hugoescalpelo/Bodies-of-Potentials/STL/Calamar - Motor Tester v3.stl

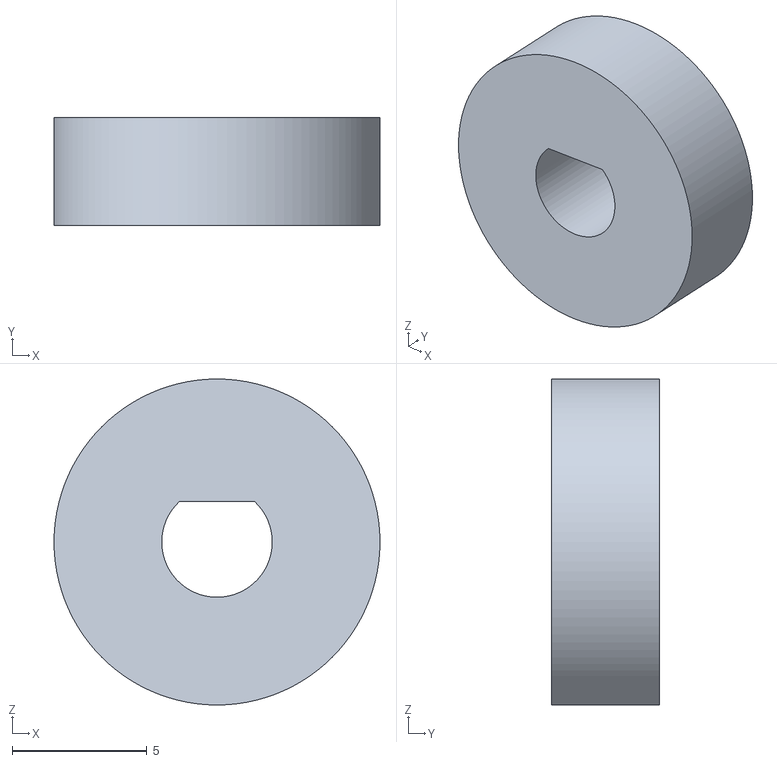
[picture p17: CAD file, 2025-03-10]
STL/Calamar - Motor Tester v3.stl
12.1 x 4.00 x 12.1
