hugoescalpelo/Bodies-of-Potentials/STL/Base Integral v26.stl

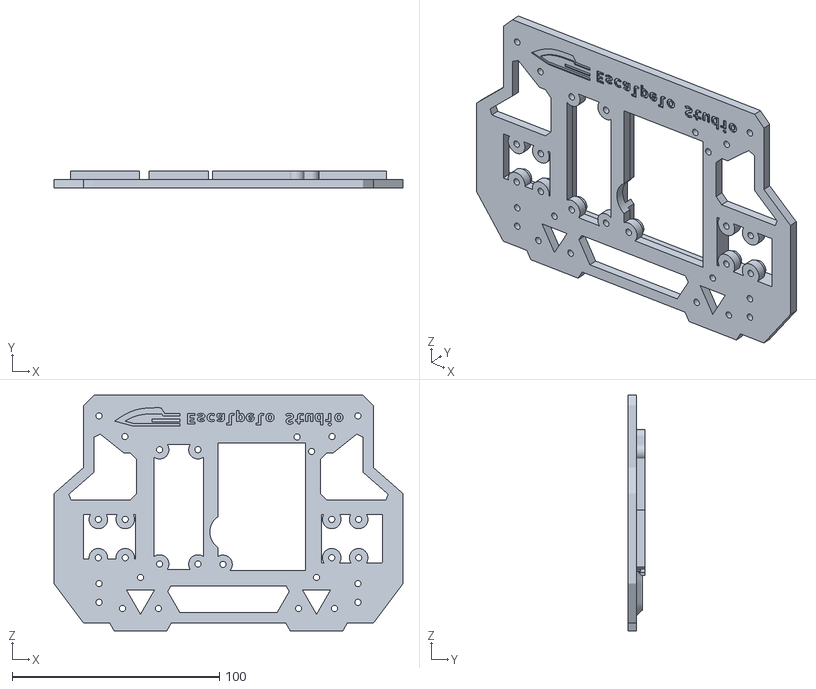
[picture p18: CAD file, 2025-03-10]
STL/Base Integral v26.stl
168.5 x 8.00 x 113.8
