hugoescalpelo/Bodies-of-Potentials/STL/Calamar_New_DC_Motor v7.stl

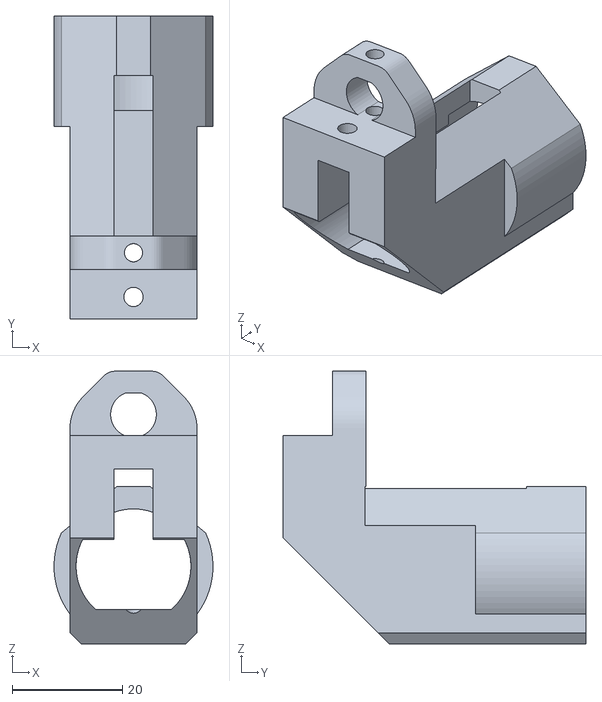
[picture p19: CAD file, 2025-03-10]
STL/Calamar_New_DC_Motor v7.stl
28.8 x 54.9 x 49.4
