hugoescalpelo/Bodies-of-Potentials/STL/plate adapter v2.stl

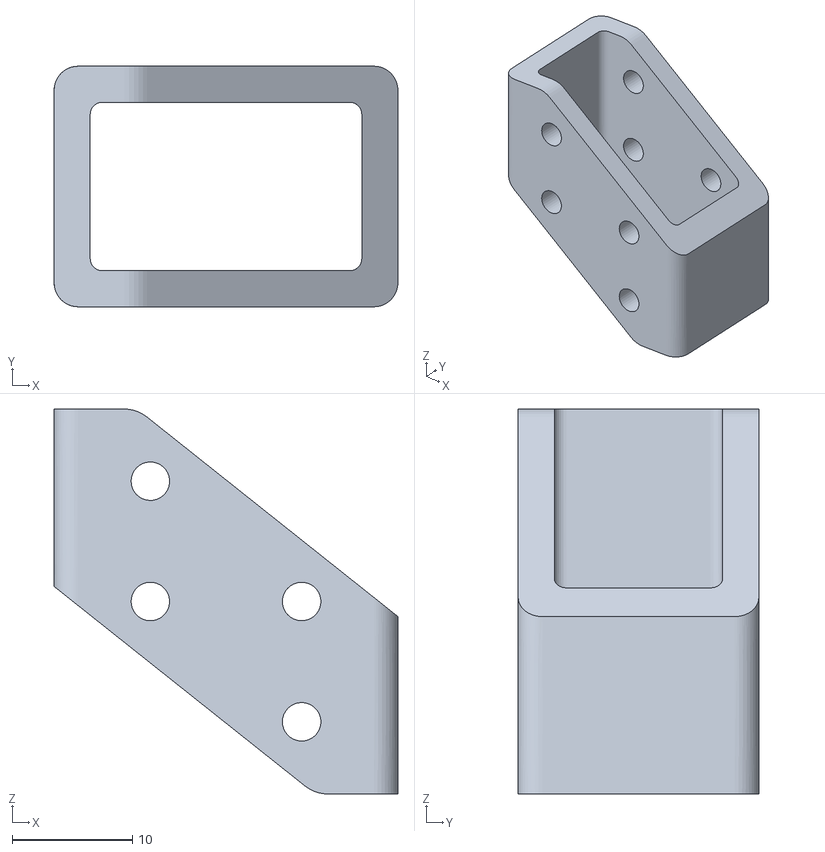
[picture p20: CAD file, 2025-03-10]
STL/plate adapter v2.stl
28.6 x 20.0 x 32.0
