hugoescalpelo/Bodies-of-Potentials/STL/Brazo nuevo Calamar.stl

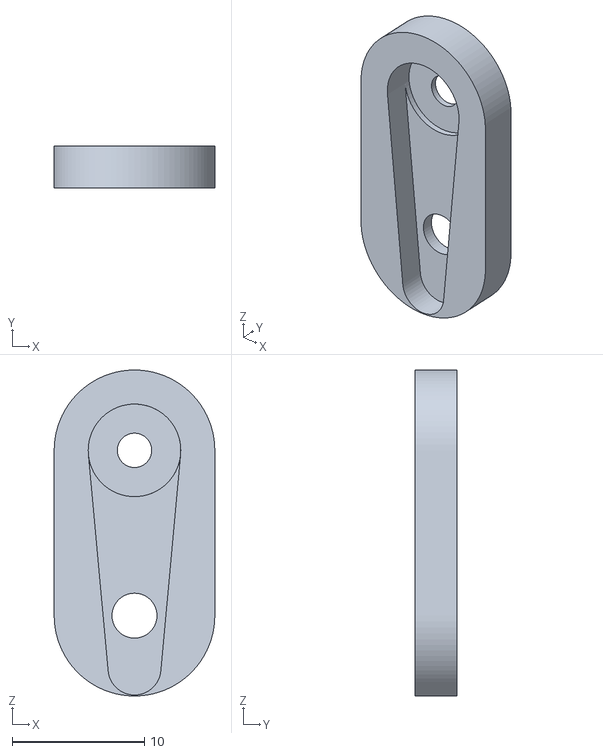
[picture p21: CAD file, 2025-03-10]
STL/Brazo nuevo Calamar.stl
12.1 x 3.20 x 24.7
